fabrizioromanelli/Pellet-Stove-Control/PCB/TantrixStoveControl.kicad_sch

## KiCad design PCB/TantrixStoveControl.kicad_sch (2026-09-04)

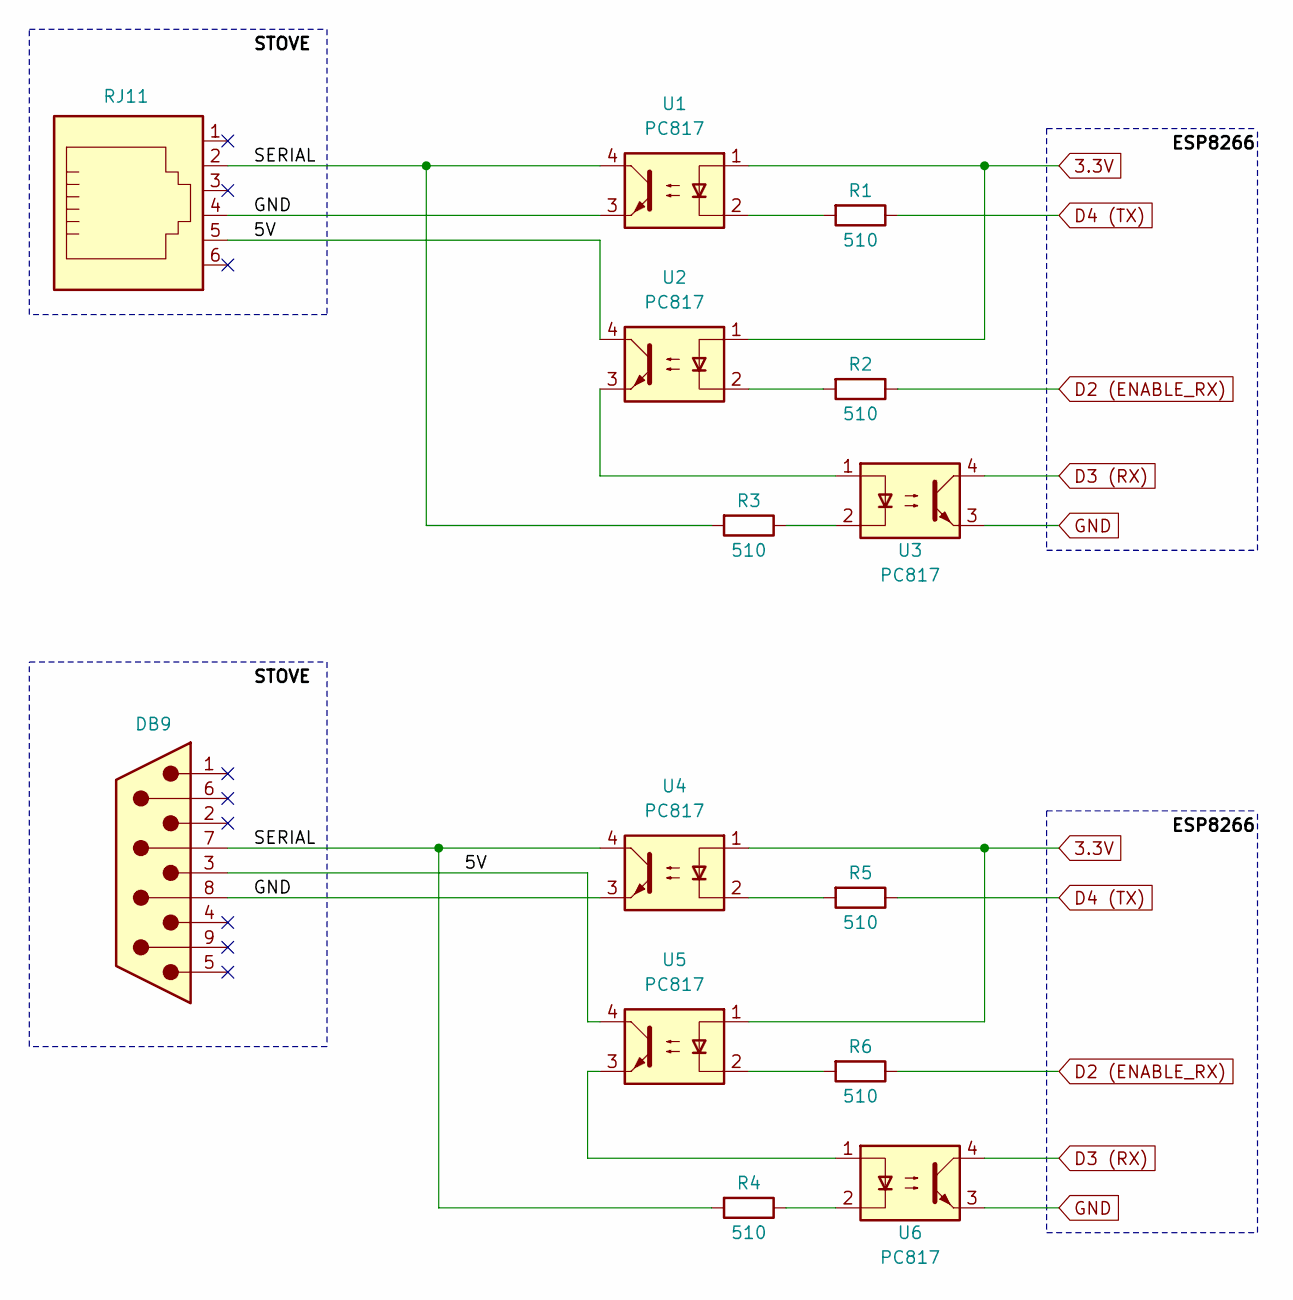
[picture p3: schematic TantrixStoveControl.kicad_sch]

Parts:
DB9: (no value)
R1, R2, R3, R4, R5, R6: 510
RJ11: Ali_RJ12
U1, U2, U3, U4, U5, U6: PC817; DIP-4_W7.62mm

Connections:
3.3V: U1.1, U2.1, U4.1, U5.1
5V: DB9.3, RJ11.5, U2.4, U5.4
D2 (ENABLE_RX): R2.1, R6.1
D3 (RX): U3.4, U6.4
D4 (TX): R1.1, R5.1
GND: DB9.8, RJ11.4, U1.3, U3.3, U4.3, U6.3
unnamed: R1.2, U1.2
unnamed: R2.2, U2.2
unnamed: R3.1, U3.2
unnamed: R4.1, U6.2
unnamed: R5.2, U4.2
unnamed: R6.2, U5.2
unnamed: U2.3, U3.1
unnamed: U5.3, U6.1
SERIAL: DB9.7, R3.2, R4.2, RJ11.2, U1.4, U4.4
